tjko/brickpico/images/falcon-back-small.jpg

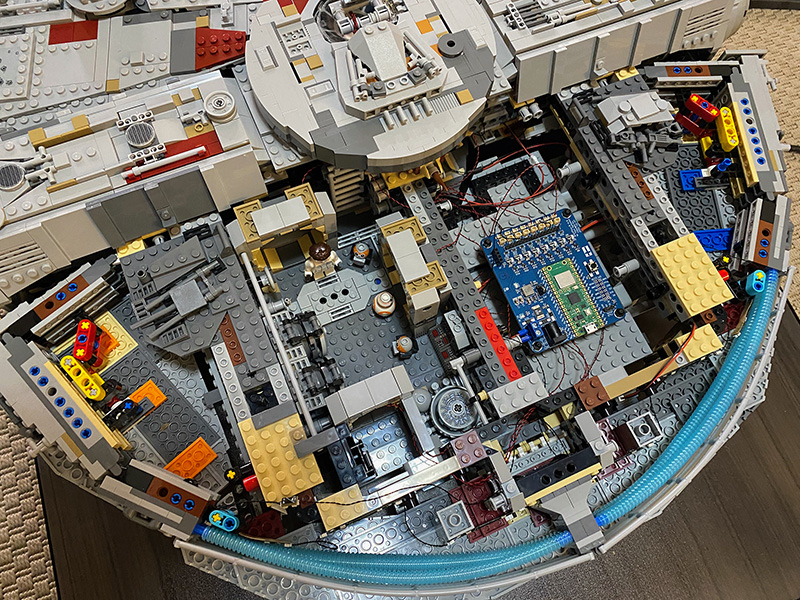
images/falcon-back-small.jpg
