tjko/brickpico/src/brickpico_fsdata.c

#include "lwip/apps/fs.h"
#include "lwip/def.h"


#define file_NULL (struct fsdata_file *) NULL


#ifndef FS_FILE_FLAGS_HEADER_INCLUDED
#define FS_FILE_FLAGS_HEADER_INCLUDED 1
#endif
#ifndef FS_FILE_FLAGS_HEADER_PERSISTENT
#define FS_FILE_FLAGS_HEADER_PERSISTENT 0
#endif
/* FSDATA_FILE_ALIGNMENT: 0=off, 1=by variable, 2=by include */
#ifndef FSDATA_FILE_ALIGNMENT
#define FSDATA_FILE_ALIGNMENT 0
#endif
#ifndef FSDATA_ALIGN_PRE
#define FSDATA_ALIGN_PRE
#endif
#ifndef FSDATA_ALIGN_POST
#define FSDATA_ALIGN_POST
#endif
#if FSDATA_FILE_ALIGNMENT==2
#include "fsdata_alignment.h"
#endif
#if FSDATA_FILE_ALIGNMENT==1
static const unsigned int dummy_align__img_brickpico_icon_png = 0;
#endif
static const unsigned char FSDATA_ALIGN_PRE data__img_brickpico_icon_png[] FSDATA_ALIGN_POST = {
/* /img/brickpico-icon.png (24 chars) */
0x2f,0x69,0x6d,0x67,0x2f,0x62,0x72,0x69,0x63,0x6b,0x70,0x69,0x63,0x6f,0x2d,0x69,
0x63,0x6f,0x6e,0x2e,0x70,0x6e,0x67,0x00,

/* HTTP header */
/* "HTTP/1.0 200 OK
" (17 bytes) */
0x48,0x54,0x54,0x50,0x2f,0x31,0x2e,0x30,0x20,0x32,0x30,0x30,0x20,0x4f,0x4b,0x0d,
0x0a,
/* "Server: BrickPico (https://github.com/tjko/brickpico)
" (55 bytes) */
0x53,0x65,0x72,0x76,0x65,0x72,0x3a,0x20,0x42,0x72,0x69,0x63,0x6b,0x50,0x69,0x63,
0x6f,0x20,0x28,0x68,0x74,0x74,0x70,0x73,0x3a,0x2f,0x2f,0x67,0x69,0x74,0x68,0x75,
0x62,0x2e,0x63,0x6f,0x6d,0x2f,0x74,0x6a,0x6b,0x6f,0x2f,0x62,0x72,0x69,0x63,0x6b,
0x70,0x69,0x63,0x6f,0x29,0x0d,0x0a,
/* "Content-Length: 2230
" (18+ bytes) */
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
0x2f,0x22,0x3e,0x0a,0x09,0x09,0x20,0x20,0x3c,0x69,0x6d,0x67,0x20,0x73,0x72,0x63,
0x3d,0x22,0x69,0x6d,0x67,0x2f,0x62,0x72,0x69,0x63,0x6b,0x70,0x69,0x63,0x6f,0x2e,
0x70,0x6e,0x67,0x22,0x20,0x62,0x6f,0x72,0x64,0x65,0x72,0x3d,0x22,0x30,0x22,0x20,
0x61,0x6c,0x74,0x3d,0x22,0x42,0x72,0x69,0x63,0x6b,0x50,0x69,0x63,0x6f,0x20,0x6c,
0x6f,0x67,0x6f,0x22,0x20,0x74,0x69,0x74,0x6c,0x65,0x3d,0x22,0x42,0x72,0x69,0x63,
0x6b,0x50,0x69,0x63,0x6f,0x20,0x6c,0x6f,0x67,0x6f,0x22,0x3e,0x0a,0x09,0x09,0x3c,
0x2f,0x61,0x3e,0x0a,0x09,0x20,0x20,0x20,0x20,0x20,0x20,0x3c,0x2f,0x74,0x64,0x3e,
0x0a,0x09,0x20,0x20,0x20,0x20,0x20,0x20,0x3c,0x74,0x64,0x20,0x63,0x6f,0x6c,0x73,
0x70,0x61,0x6e,0x3d,0x22,0x32,0x22,0x20,0x76,0x61,0x6c,0x69,0x67,0x6e,0x3d,0x22,
0x62,0x6f,0x74,0x74,0x6f,0x6d,0x22,0x3e,0x0a,0x09,0x09,0x3c,0x68,0x32,0x3e,0x3c,
0x66,0x6f,0x6e,0x74,0x20,0x63,0x6f,0x6c,0x6f,0x72,0x3d,0x22,0x23,0x30,0x33,0x61,
0x33,0x61,0x61,0x22,0x3e,0x42,0x72,0x69,0x63,0x6b,0x50,0x69,0x63,0x6f,0x3a,0x20,
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



const struct fsdata_file file__img_brickpico_icon_png[] = { {
file_NULL,
data__img_brickpico_icon_png,
data__img_brickpico_icon_png + 24,
sizeof(data__img_brickpico_icon_png) - 24,
FS_FILE_FLAGS_HEADER_INCLUDED | FS_FILE_FLAGS_HEADER_PERSISTENT,
}};

const struct fsdata_file file__img_brickpico_png[] = { {
file__img_brickpico_icon_png,
data__img_brickpico_png,
data__img_brickpico_png + 20,
sizeof(data__img_brickpico_png) - 20,
FS_FILE_FLAGS_HEADER_INCLUDED | FS_FILE_FLAGS_HEADER_PERSISTENT,
}};

const struct fsdata_file file__303_main[] = { {
file__img_brickpico_png,
data__303_main,
data__303_main + 12,
sizeof(data__303_main) - 12,
FS_FILE_FLAGS_HEADER_INCLUDED | FS_FILE_FLAGS_HEADER_PERSISTENT,
}};

const struct fsdata_file file__404_html[] = { {
file__303_main,
data__404_html,
data__404_html + 12,
sizeof(data__404_html) - 12,
FS_FILE_FLAGS_HEADER_INCLUDED | FS_FILE_FLAGS_HEADER_PERSISTENT,
}};

const struct fsdata_file file__brickpico_16_shtml[] = { {
file__404_html,
data__brickpico_16_shtml,
data__brickpico_16_shtml + 20,
sizeof(data__brickpico_16_shtml) - 20,
FS_FILE_FLAGS_HEADER_INCLUDED | FS_FILE_FLAGS_SSI,
}};

const struct fsdata_file file__brickpico_8_shtml[] = { {
file__brickpico_16_shtml,
data__brickpico_8_shtml,
data__brickpico_8_shtml + 20,
sizeof(data__brickpico_8_shtml) - 20,
FS_FILE_FLAGS_HEADER_INCLUDED | FS_FILE_FLAGS_SSI,
}};

const struct fsdata_file file__brickpico_css[] = { {
file__brickpico_8_shtml,
data__brickpico_css,
data__brickpico_css + 16,
sizeof(data__brickpico_css) - 16,
FS_FILE_FLAGS_HEADER_INCLUDED | FS_FILE_FLAGS_HEADER_PERSISTENT,
}};

const struct fsdata_file file__status_csv[] = { {
file__brickpico_css,
data__status_csv,
data__status_csv + 12,
sizeof(data__status_csv) - 12,
FS_FILE_FLAGS_HEADER_INCLUDED | FS_FILE_FLAGS_SSI,
}};

const struct fsdata_file file__status_json[] = { {
file__status_csv,
data__status_json,
data__status_json + 16,
sizeof(data__status_json) - 16,
FS_FILE_FLAGS_HEADER_INCLUDED | FS_FILE_FLAGS_SSI,
}};

const struct fsdata_file file__status_shtml[] = { {
file__status_json,
data__status_shtml,
data__status_shtml + 16,
sizeof(data__status_shtml) - 16,
FS_FILE_FLAGS_HEADER_INCLUDED | FS_FILE_FLAGS_SSI,
}};

#define FS_ROOT file__status_shtml
#define FS_NUMFILES 10
