tjko/brickpico/src/bi_decl.c

/* bi_decl.c
   Copyright (C) 2023-2025 Timo Kokkonen <tjko@iki.fi>

   SPDX-License-Identifier: GPL-3.0-or-later

   This file is part of BrickPico.

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
   You should have received a copy of the GNU General Public License
   along with BrickPico. If not, see <https://www.gnu.org/licenses/>.
*/

#include "pico/stdlib.h"
#include "pico/binary_info.h"

#include "brickpico.h"

#define BI_TAG           0xf720
#define BOOT_SETTINGS    0x0001


void set_binary_info(struct brickpico_fw_settings *settings)
{
	bi_decl(bi_program_description("BrickPico-" BRICKPICO_MODEL " - Smart LED Controller"));
	bi_decl(bi_program_version_string(BRICKPICO_VERSION BRICKPICO_BUILD_TAG));
	bi_decl(bi_program_build_date_string("__DATE__"));
	bi_decl(bi_program_url("https://github.com/tjko/brickpico/"));

	bi_decl(bi_program_feature_group(BI_TAG, BOOT_SETTINGS, "boot settings"));
	bi_decl(bi_ptr_int32(BI_TAG, BOOT_SETTINGS, safemode, 0));
	bi_decl(bi_ptr_int32(BI_TAG, BOOT_SETTINGS, bootdelay, 0));
	settings->safemode = safemode;
	settings->bootdelay = bootdelay;

        bi_decl(bi_block_device(
			BI_TAG,
			"littlefs",
			XIP_BASE + BRICKPICO_FS_OFFSET,
			BRICKPICO_FS_SIZE,
			NULL,
			BINARY_INFO_BLOCK_DEV_FLAG_READ
			| BINARY_INFO_BLOCK_DEV_FLAG_WRITE
			| BINARY_INFO_BLOCK_DEV_FLAG_PT_NONE));

#if LED_PIN >= 0
	bi_decl(bi_1pin_with_name(LED_PIN, "On-board LED (output)"));
#endif

#if TX_PIN >= 0
	bi_decl(bi_1pin_with_name(TX_PIN, "TX (Serial)"));
	bi_decl(bi_1pin_with_name(RX_PIN, "RX (Serial)"));
#endif
#if SDA_PIN >= 0
	bi_decl(bi_1pin_with_name(SDA_PIN, "SDA (I2C)"));
	bi_decl(bi_1pin_with_name(SCL_PIN, "SCL (I2C)"));
#endif

#if SCK_PIN >= 0
	bi_decl(bi_1pin_with_name(SCK_PIN, "SCK (SPI)"));
	bi_decl(bi_1pin_with_name(MOSI_PIN, "MOSI (SPI)"));
	bi_decl(bi_1pin_with_name(MISO_PIN, "MISO (SPI)"));
	bi_decl(bi_1pin_with_name(CS_PIN, "CS (SPI)"));
#endif
#if DC_PIN >= 0
	bi_decl(bi_1pin_with_name(DC_PIN, "LCD DC (SPI)"));
#endif
#if LCD_RESET_PIN >= 0
	bi_decl(bi_1pin_with_name(LCD_RESET_PIN, "LCD Reset (SPI)"));
#endif
#if LCD_LIGHT_PIN >= 0
	bi_decl(bi_1pin_with_name(LCD_LIGHT_PIN, "LCD Backlight (SPI)"));
#endif

	bi_decl(bi_1pin_with_name(PWM1_PIN, "PWM1 signal (output)"));
	bi_decl(bi_1pin_with_name(PWM2_PIN, "PWM2 signal (output)"));
	bi_decl(bi_1pin_with_name(PWM3_PIN, "PWM3 signal (output)"));
	bi_decl(bi_1pin_with_name(PWM4_PIN, "PWM4 signal (output)"));
	bi_decl(bi_1pin_with_name(PWM5_PIN, "PWM5 signal (output)"));
	bi_decl(bi_1pin_with_name(PWM6_PIN, "PWM6 signal (output)"));
	bi_decl(bi_1pin_with_name(PWM7_PIN, "PWM7 signal (output)"));
	bi_decl(bi_1pin_with_name(PWM8_PIN, "PWM8 signal (output)"));
#if PWM9_PIN >= 0
	bi_decl(bi_1pin_with_name(PWM9_PIN, "PWM9 signal (output)"));
	bi_decl(bi_1pin_with_name(PWM10_PIN, "PWM10 signal (output)"));
	bi_decl(bi_1pin_with_name(PWM11_PIN, "PWM11 signal (output)"));
	bi_decl(bi_1pin_with_name(PWM12_PIN, "PWM12 signal (output)"));
	bi_decl(bi_1pin_with_name(PWM13_PIN, "PWM13 signal (output)"));
	bi_decl(bi_1pin_with_name(PWM14_PIN, "PWM14 signal (output)"));
	bi_decl(bi_1pin_with_name(PWM15_PIN, "PWM15 signal (output)"));
	bi_decl(bi_1pin_with_name(PWM16_PIN, "PWM16 signal (output)"));
#endif
}
