tjko/brickpico/src/effects.c

/* effects.c
   Copyright (C) 2025 Timo Kokkonen <tjko@iki.fi>

   SPDX-License-Identifier: GPL-3.0-or-later

   This file is part of BrickPico.

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
   You should have received a copy of the GNU General Public License
   along with BrickPico. If not, see <https://www.gnu.org/licenses/>.
*/

#include <stdio.h>
#include <stdlib.h>
#include <string.h>
#include "pico/stdlib.h"

#include "brickpico.h"


/* effects_fade.c */
void* effect_fade_parse_args(const char *args);
char* effect_fade_print_args(void *ctx);
uint8_t effect_fade(void *ctx, uint64_t t_now, uint8_t pwm, uint8_t pwr);

/* effects_blink.c */
void* effect_blink_parse_args(const char *args);
char* effect_blink_print_args(void *ctx);
uint8_t effect_blink(void *ctx, uint64_t t_now, uint8_t pwm, uint8_t pwr);

/* effects_pulse.c */
void* effect_pulse_parse_args(const char *args);
char* effect_pulse_print_args(void *ctx);
uint8_t effect_pulse(void *ctx, uint64_t t_now, uint8_t pwm, uint8_t pwr);


static const effect_entry_t effects[] = {
	{ "none", NULL, NULL, NULL }, /* EFFECT_NONE */
	{ "fade", effect_fade_parse_args, effect_fade_print_args, effect_fade }, /* EFFECT_FADE */
	{ "blink", effect_blink_parse_args, effect_blink_print_args, effect_blink }, /* EFFECT_BLINK */
	{ "pulse", effect_pulse_parse_args, effect_pulse_print_args, effect_pulse }, /* EFFECT_PULSE */
	{ NULL, NULL, NULL, NULL }
};



int str2effect(const char *s)
{
	int ret = EFFECT_NONE;

	for(int i = 0; effects[i].name; i++) {
		if (!strncasecmp(s, effects[i].name, strlen(effects[i].name) + 1)) {
			ret = i;
			break;
		}
	}

	return ret;
}


const char* effect2str(enum light_effect_types effect)
{
	if (effect <= EFFECT_ENUM_MAX) {
		return effects[effect].name;
	}

	return "none";
}


void* effect_parse_args(enum light_effect_types effect, const char *args)
{
	void *ret = NULL;

	if (effect <= EFFECT_ENUM_MAX) {
		if (effects[effect].parse_args_func)
			ret = effects[effect].parse_args_func(args);
	}

	return ret;
}


char* effect_print_args(enum light_effect_types effect, void *ctx)
{
	char *ret = NULL;

	if (effect <= EFFECT_ENUM_MAX && ctx) {
		if (effects[effect].print_args_func)
			ret = effects[effect].print_args_func(ctx);
	}

	return ret;
}


inline uint8_t light_effect(enum light_effect_types effect, void *ctx, uint64_t t, uint8_t pwm, uint8_t pwr)
{
	uint8_t ret = 0;

	if (effect <= EFFECT_ENUM_MAX) {
		if (effects[effect].effect_func)
			ret = effects[effect].effect_func(ctx, t, pwm, pwr);
		else
			ret = (pwr ? pwm : 0);
	}

	return ret;
}


/* eof :-) */
