tjko/brickpico/src/ssh_util.c

/* ssh_util.c
   Copyright (C) 2025 Timo Kokkonen <tjko@iki.fi>

   SPDX-License-Identifier: GPL-3.0-or-later

   This file is part of BrickPico.

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
   You should have received a copy of the GNU General Public License
   along with BrickPico. If not, see <https://www.gnu.org/licenses/>.
*/

#include <stdio.h>
#include <string.h>
#include <wolfssl/wolfcrypt/wc_port.h>
#include <wolfssl/wolfcrypt/asn.h>
#include <wolfssh/keygen.h>
#include <pico-sshd.h>

#include "brickpico.h"


typedef struct ssh_pkey_alg_t {
	char *name;
	char *filename;
	int (*create_key)(void *buf, size_t buf_size);
} ssh_pkey_alg_t;



#ifndef NO_RSA
static int create_rsa_key(void *buf, size_t buf_size)
{
	return wolfSSH_MakeRsaKey(buf, buf_size, WOLFSSH_RSAKEY_DEFAULT_SZ,
		WOLFSSH_RSAKEY_DEFAULT_E);
}
#endif


static int create_ecdsa_key(void *buf, size_t buf_size)
{
	return wolfSSH_MakeEcdsaKey(buf, buf_size, WOLFSSH_ECDSAKEY_PRIME256);
}


static int create_ed25519_key(void *buf, size_t buf_size)
{
    WC_RNG rng;
    ed25519_key key;
    int ret = WS_SUCCESS;
    int key_size;

    if (wc_InitRng(&rng))
	return WS_CRYPTO_FAILED;

    if (wc_ed25519_init(&key))
            ret = WS_CRYPTO_FAILED;

    if (ret == WS_SUCCESS) {
            ret = wc_ed25519_make_key(&rng, 256/8, &key);
            if (ret)
		    ret = WS_CRYPTO_FAILED;
            else
		    ret = WS_SUCCESS;
    }

    if (ret == WS_SUCCESS) {
            if ((key_size = wc_Ed25519KeyToDer(&key, buf, buf_size)) < 0)
                    ret = WS_CRYPTO_FAILED;
            else
		    ret = key_size;
        }

    wc_ed25519_free(&key);

    if (wc_FreeRng(&rng))
            ret = WS_CRYPTO_FAILED;

    return ret;
}


static const ssh_pkey_alg_t pkey_algorithms[] = {
	{ "ecdsa", "ssh-ecdsa.der", create_ecdsa_key },
	{ "ed25519", "ssh-ed25519.der", create_ed25519_key },
#ifndef NO_RSA
	{ "rsa", "ssh-rsa.der", create_rsa_key },
#endif
	{ NULL, NULL, NULL }
};



void ssh_list_pkeys()
{
	char *buf = NULL;
	char tmp[64];
	uint32_t buf_size = 0;
	int i = 0;

	while(pkey_algorithms[i].name) {
		const ssh_pkey_alg_t *alg = &pkey_algorithms[i++];
		int res = flash_read_file(&buf, &buf_size, alg->filename);

		printf("%-20s ", alg->name);
		if (res == 0) {
			printf("%8lu SHA256:%s\n", buf_size,
				ssh_server_get_pubkey_hash(buf, buf_size, tmp, sizeof(tmp)));
			free(buf);
		} else {
			printf("<No Key>\n");
		}
	}
}


int ssh_create_pkey(const char* args)
{
	const size_t buf_size = 4096;
	int kcount = 0;
	bool create_all = false;
	byte *buf;
	int res;


	if (!strncasecmp(args, "all", 4))
		create_all = true;

	for (int i = 0; pkey_algorithms[i].name; i++) {
		const ssh_pkey_alg_t *alg = &pkey_algorithms[i];

		if (!create_all && strncasecmp(args, alg->name, strlen(alg->name) + 1))
			continue;

		if (flash_file_size(alg->filename) > 0) {
			printf("%s key already exists!\n", alg->name);
			continue;
		}

		printf("Generating %s private key...", alg->name);
		if (!(buf = calloc(1, buf_size))) {
			printf("Out or memory!\n");
				return 2;
		}
		res = alg->create_key(buf, buf_size);
		if (res > 0) {
			res = flash_write_file((const char*)buf, res, alg->filename);
			if (res) {
				printf("Failed to save private key! (%d)\n", res);
			} else {
				printf("OK\n");
				kcount++;
			}
		} else {
			printf("Failed to generate key! (%d)\n", res);
		}
		free(buf);
	}

	return (kcount > 0 ? 0 : 1);
}


int ssh_delete_pkey(const char* args)
{
	int res;


	for (int i = 0; pkey_algorithms[i].name; i++) {
		const ssh_pkey_alg_t *alg = &pkey_algorithms[i];

		if (!strncasecmp(args, alg->name, strlen(alg->name) + 1)) {
			printf("Deleting %s private key...\n", alg->name);
			res = flash_delete_file(alg->filename);
			if (res == -2) {
				printf("No private key present.\n");
				res = 0;
			}
			else if (res) {
				printf("Failed to delete private key: %d\n", res);
				res = 2;
			} else {
				printf("Private key deleted.\n");
			}

			return res;
		}
	}

	return 1;
}


int ssh_get_pkey(int index, char** buf_ptr, uint32_t* buf_size_ptr, const char** name_ptr)
{
	if (index < 0 || !buf_ptr || !buf_size_ptr || !name_ptr)
		return -1;

	*name_ptr = "";

	/* Find the key... */
	for (int i = 0; pkey_algorithms[i].name; i++) {
		const ssh_pkey_alg_t *alg = &pkey_algorithms[i];

		if (i != index)
			continue;

		if (flash_read_file(buf_ptr, buf_size_ptr, alg->filename)) {
			/* No key found... */
			return 0;
		}

		/* Found the key... */
		log_msg(LOG_DEBUG, "Found SSH private key: %s (%lu)",
			alg->filename, *buf_size_ptr);
		*name_ptr = alg->name;
		return 1;
	}

	return -2;
}

/* eof :-) */
